whati001/morgeb/frontpanel/frontLayoutEN.png

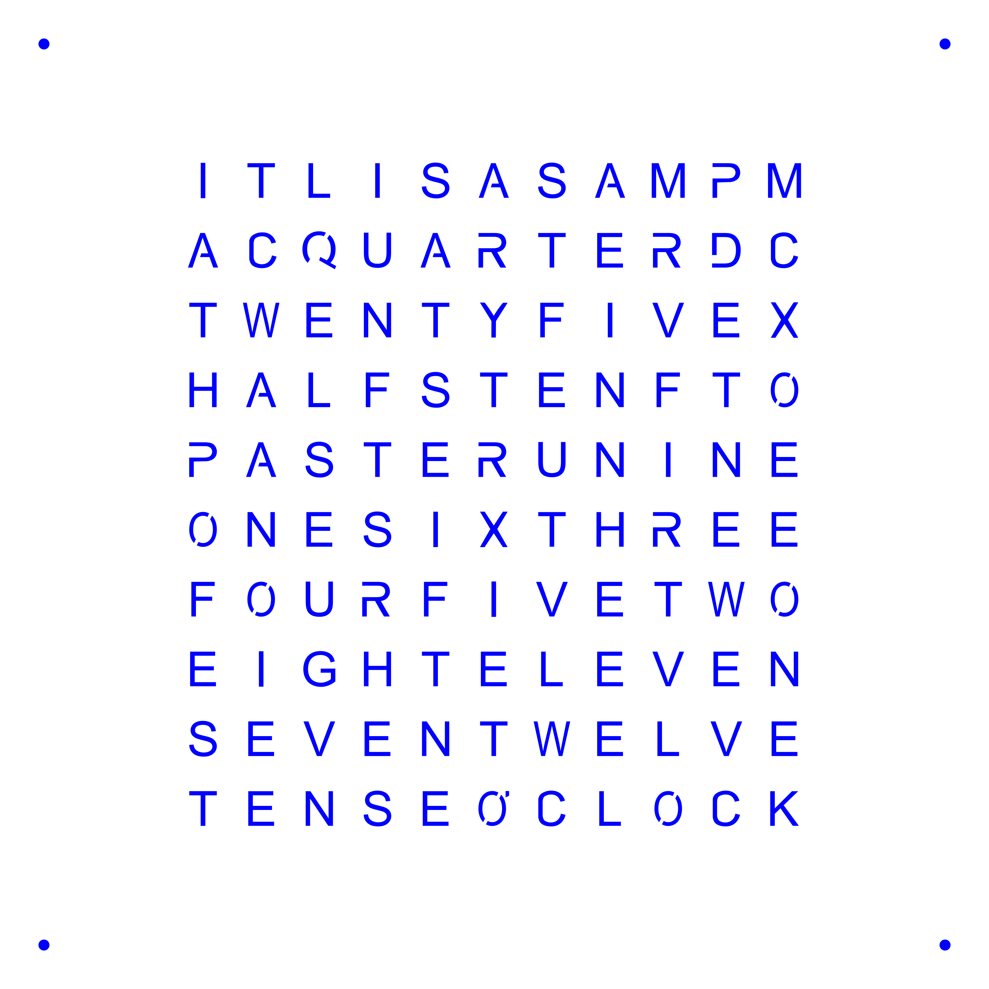
frontpanel/frontLayoutEN.png
